arachnidlabs/loki/drawings/Dimensional Drawing.PNG

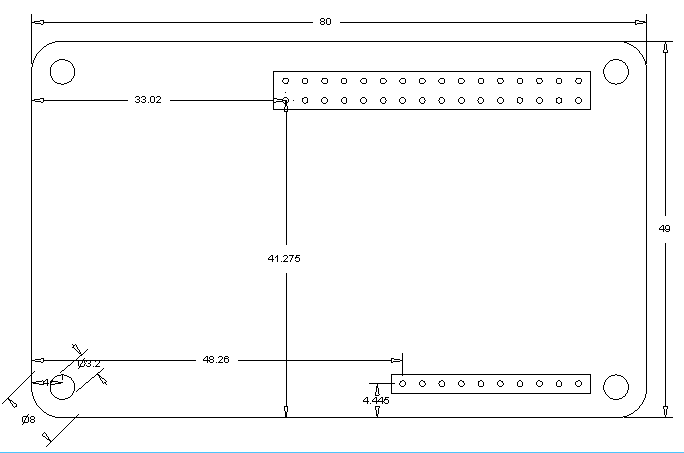
drawings/Dimensional Drawing.PNG
