arachnidlabs/loki/schematics/currentplank/currentplank-layout.png

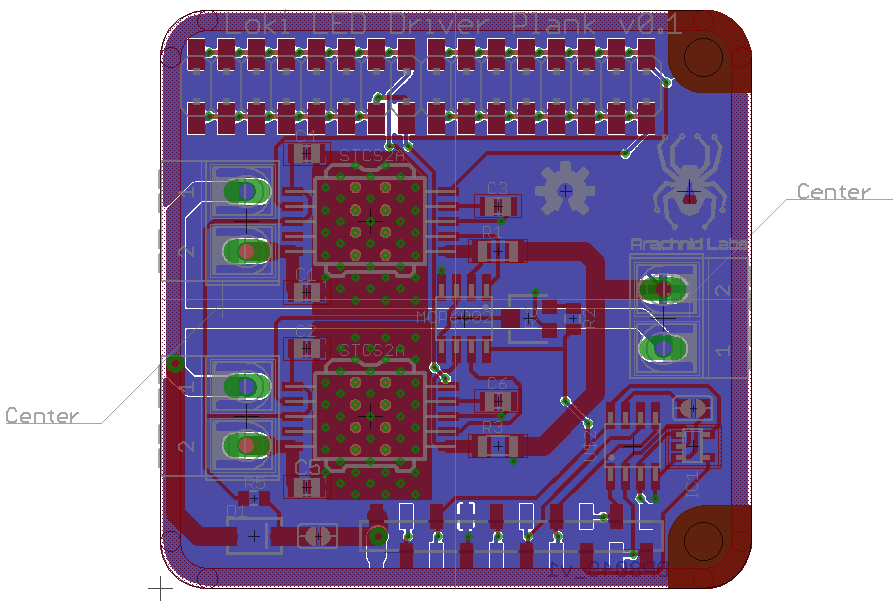
schematics/currentplank/currentplank-layout.png
