arachnidlabs/loki/schematics/currentplank/currentplank-schematic.png

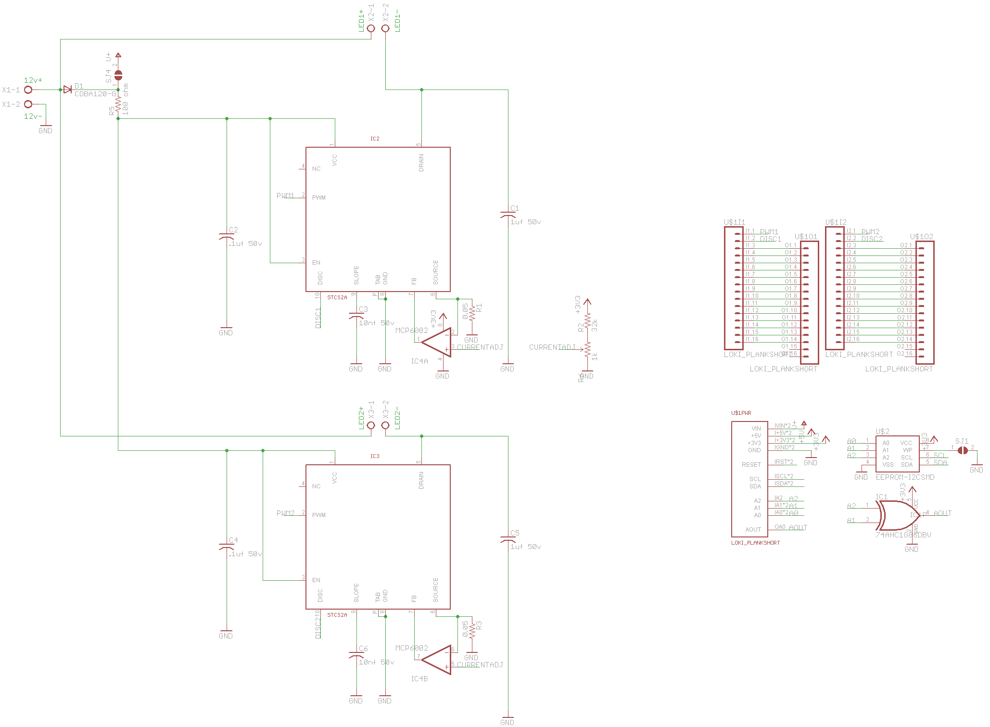
schematics/currentplank/currentplank-schematic.png
