arachnidlabs/loki/schematics/displayplank/displayplank-layout.png

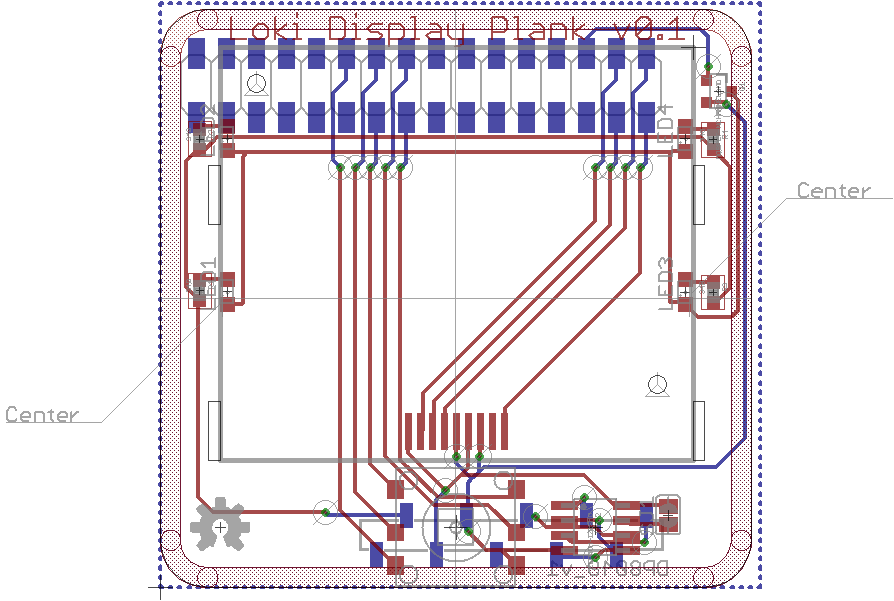
schematics/displayplank/displayplank-layout.png
