arachnidlabs/loki/schematics/loki/loki-layout.png

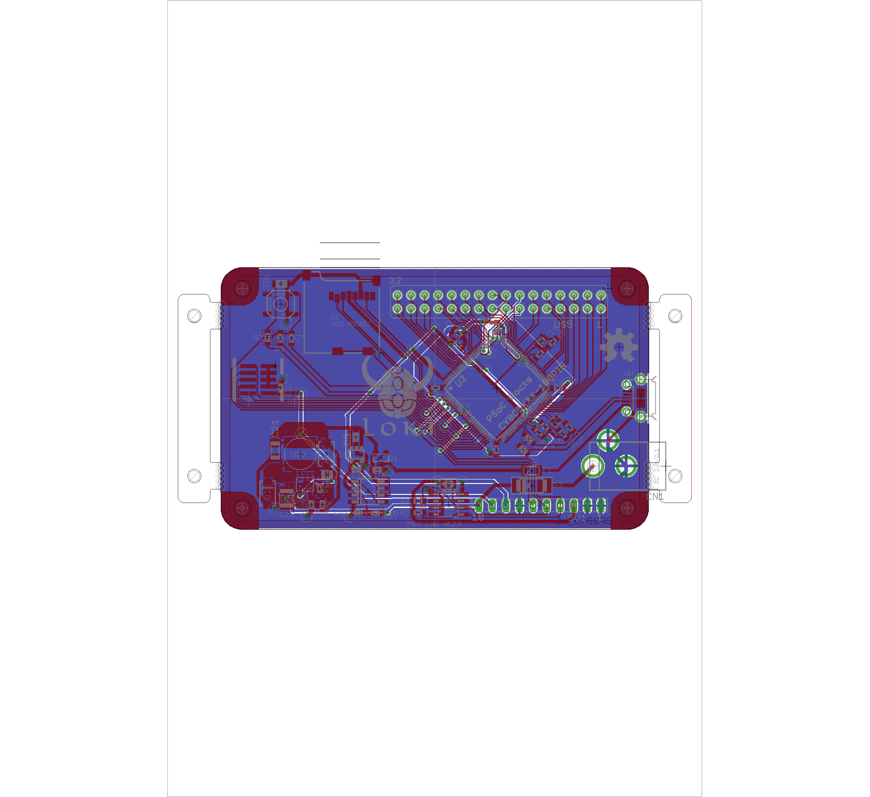
schematics/loki/loki-layout.png
