arachnidlabs/loki/schematics/programmer/programmer-layout.png

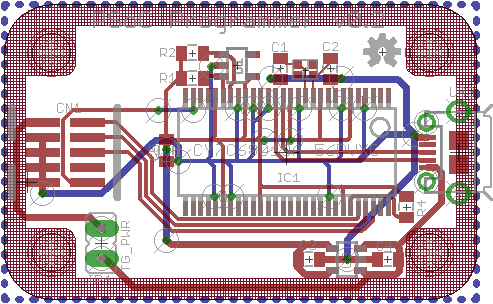
schematics/programmer/programmer-layout.png
