arachnidlabs/loki/schematics/protoplank/protoplank-schematic.png

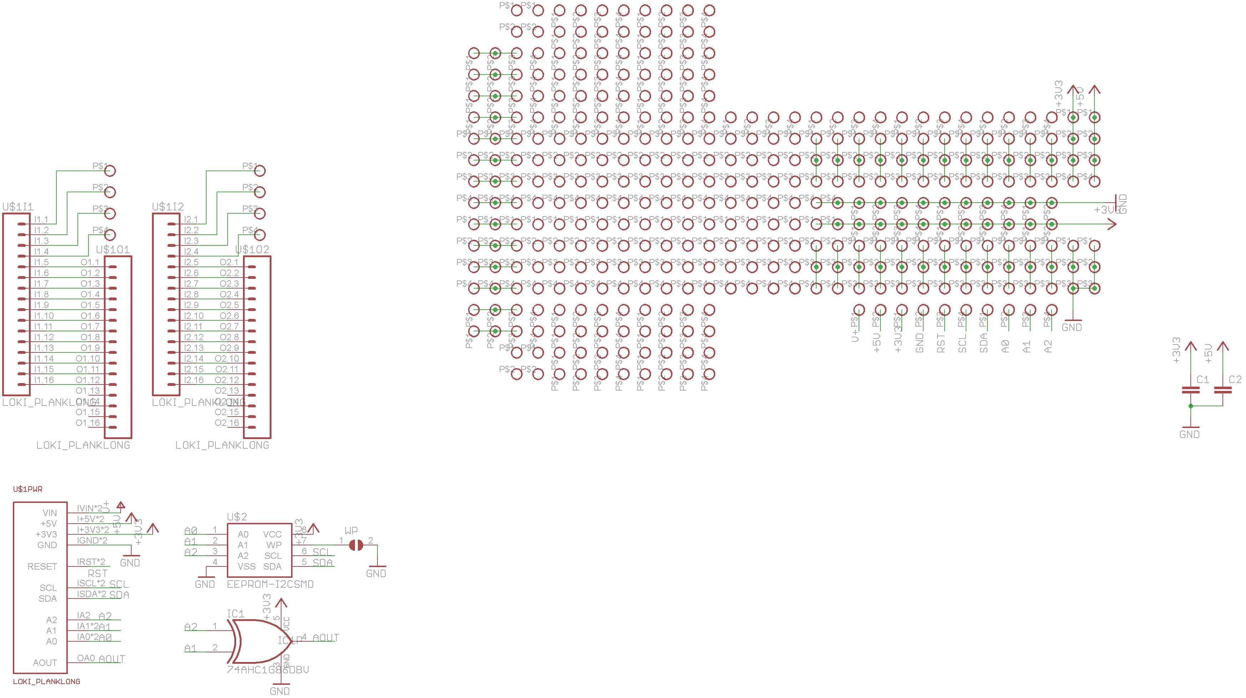
schematics/protoplank/protoplank-schematic.png
