arachnidlabs/loki/schematics/shieldplank/shieldplank-layout.png

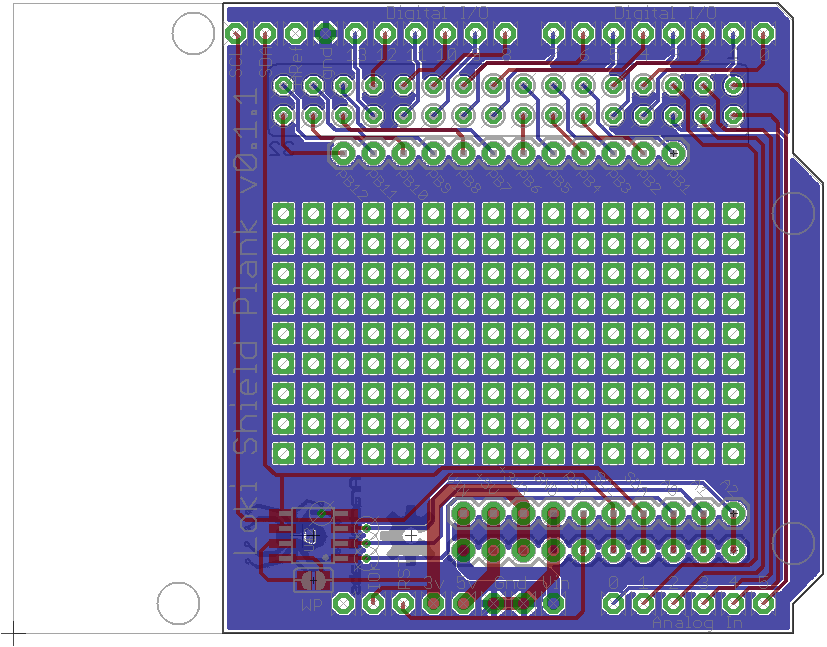
schematics/shieldplank/shieldplank-layout.png
