arachnidlabs/loki/schematics/shieldplank/shieldplank-schematic.png

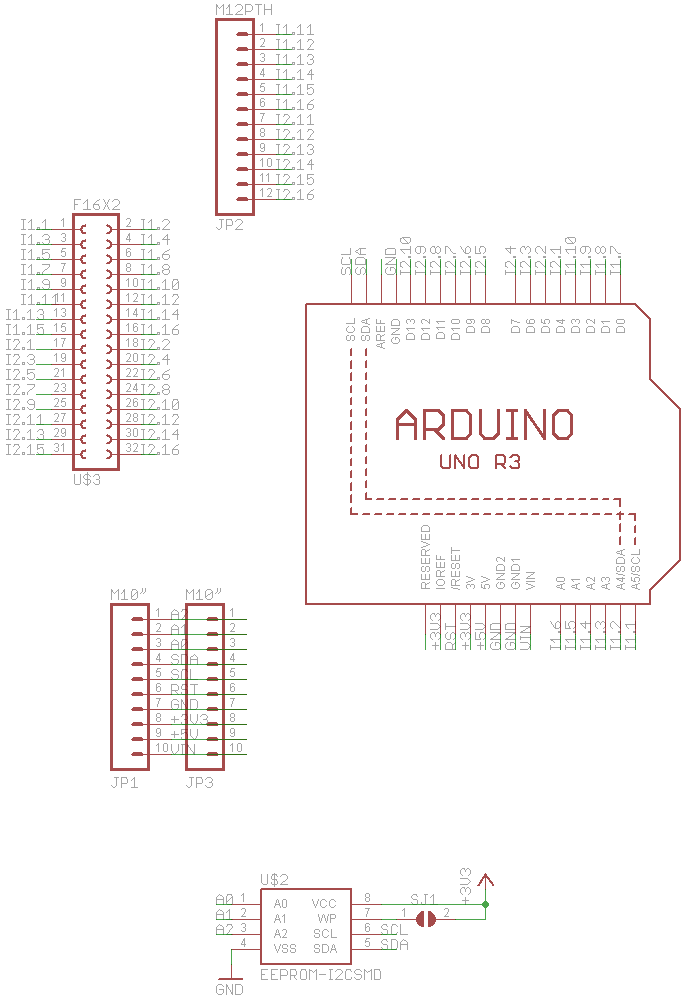
schematics/shieldplank/shieldplank-schematic.png
