arachnidlabs/loki/schematics/soundplank/soundplank-layout.png

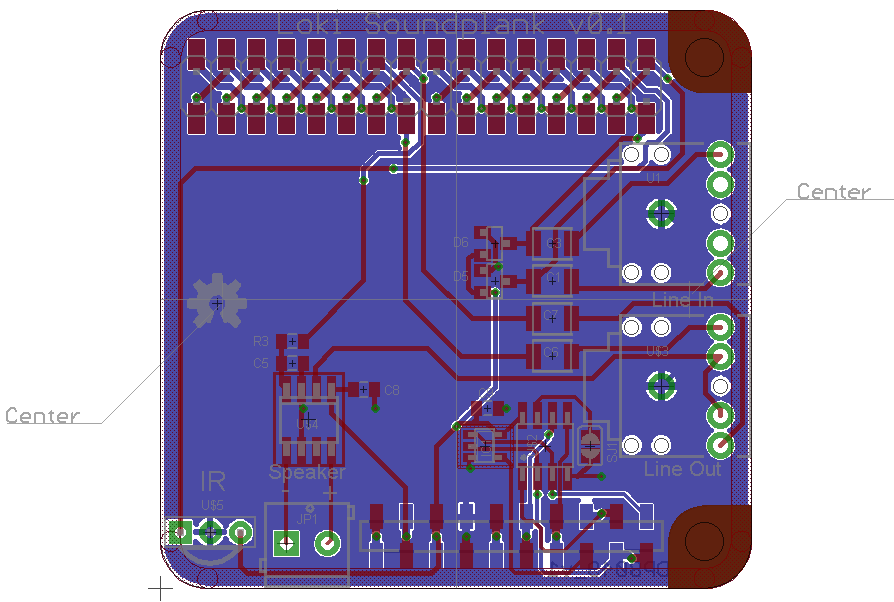
schematics/soundplank/soundplank-layout.png
